GiuseppeLeotta/SkyClock32/tools/IMG_P1.jpg

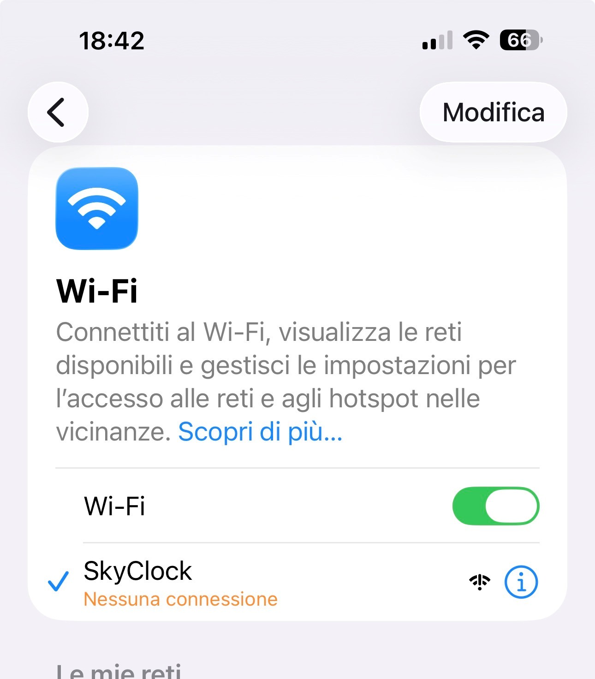
tools/IMG_P1.jpg
