GiuseppeLeotta/SkyClock32/SkyClock32/dataJupiterImg.h

#ifndef _DATA_JUPITER_IMG_H_
#define _DATA_JUPITER_IMG_H_

#include "gImage.h"

// Immagine convertita in RGB565 (148x148)
const uint16_t jupiterImg[21904] PROGMEM = {
0x0BB4, 0x0BB4, 0x0BB4, 0x0BB4, 0x0BB4, 0x0BB4, 0x0BB4, 0x0BB4, 0x0BB4, 0x0BB4, 0x0BB4, 0x0BB4, 0x0BB4, 0x0BB4, 0x0BB4, 0x0BB4, 
0x0BB4, 0x0BB4, 0x0BB4, 0x0BB4, 0x0BB4, 0x0BB4, 0x0BB4, 0x0BB4, 0x0BB4, 0x0BB4, 0x0BB4, 0x0BB4, 0x0BB4, 0x0BB4, 0x0BB4, 0x0BB4, 
0x0BB4, 0x0BB4, 0x0BB4, 0x0BB4, 0x0BB4, 0x0BB4, 0x0BB4, 0x0BB4, 0x0BB4, 0x0BB4, 0x0BB4, 0x0BB4, 0x0BB4, 0x0BB4, 0x0BB4, 0x0BB4, 
0x0BB4, 0x0BB4, 0x0BB4, 0x0BB4, 0x0BB4, 0x0BB4, 0x0BB4, 0x0BB4, 0x0BB4, 0x0BB4, 0x0BB4, 0x0BB4, 0x0BB4, 0x0BB4, 0x0BB4, 0x0BB4, 
0x0BB4, 0x0BB4, 0x0BB4, 0x0BB4, 0x0BB4, 0x0BB4, 0x0BB4, 0x0BB4, 0x0BB4, 0x0BB4, 0x0BB4, 0x0BB4, 0x0BB4, 0x0BB4, 0x0BB4, 0x0BB4, 
0x0BB4, 0x0BB4, 0x0BB4, 0x0BB4, 0x0BB4, 0x0BB4, 0x0BB4, 0x0BB4, 0x0BB4, 0x0BB4, 0x0BB4, 0x0BB4, 0x0BB4, 0x0BB4, 0x0BB4, 0x0BB4, 
0x0BB4, 0x0BB4, 0x0BB4, 0x0BB4, 0x0BB4, 0x0BB4, 0x0BB4, 0x0BB4, 0x0BB4, 0x0BB4, 0x0BB4, 0x0BB4, 0x0BB4, 0x0BB4, 0x0BB4, 0x0BB4, 
0x0BB4, 0x0BB4, 0x0BB4, 0x0BB4, 0x0BB4, 0x0BB4, 0x0BB4, 0x0BB4, 0x0BB4, 0x0BB4, 0x0BB4, 0x0BB4, 0x0BB4, 0x0BB4, 0x0BB4, 0x0BB4, 
0x0BB4, 0x0BB4, 0x0BB4, 0x0BB4, 0x0BB4, 0x0BB4, 0x0BB4, 0x0BB4, 0x0BB4, 0x0BB4, 0x0BB4, 0x0BB4, 0x0BB4, 0x0BB4, 0x0BB4, 0x0BB4, 
0x0BB4, 0x0BB4, 0x0BB4, 0x0BB4, 0x0BB4, 0x0BB4, 0x0BB4, 0x0BB4, 0x0BB4, 0x0BB4, 0x0BB4, 0x0BB4, 0x0BB4, 0x0BB4, 0x0BB4, 0x0BB4, 
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
0x0BB4, 0x0BB4, 0x0BB4, 0x0BB4, 0x0BB4, 0x0BB4, 0x0BB4, 0x0BB4, 0x0BB4, 0x0BB4, 0x0BB4, 0x0BB4, 0x0BB4, 0x0BB4, 0x0BB4, 0x0BB4, 
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

};


gImage jupiterImage {
   148,148, (uint16_t *) jupiterImg
};

#endif
