GiuseppeLeotta/SkyClock32/SkyClock32/dataMercuryImg.h

#ifndef _DATA_MERCURY_IMG_H_
#define _DATA_MERCURY_IMG_H_

#include "gImage.h"

// Immagine convertita in RGB565 (148x148)
const uint16_t mercuryImg[21904] PROGMEM = {
0x0BB4, 0x0BB4, 0x0BB4, 0x0BB4, 0x0BB4, 0x0BB4, 0x0BB4, 0x0BB4, 0x0BB4, 0x0BB4, 0x0BB4, 0x0BB4, 0x0BB4, 0x0BB4, 0x0BB4, 0x0BB4, 
0x0BB4, 0x0BB4, 0x0BB4, 0x0BB4, 0x0BB4, 0x0BB4, 0x0BB4, 0x0BB4, 0x0BB4, 0x0BB4, 0x0BB4, 0x0BB4, 0x0BB4, 0x0BB4, 0x0BB4, 0x0BB4, 
0x0BB4, 0x0BB4, 0x0BB4, 0x0BB4, 0x0BB4, 0x0BB4, 0x0BB4, 0x0BB4, 0x0BB4, 0x0BB4, 0x0BB4, 0x0BB4, 0x0BB4, 0x0BB4, 0x0BB4, 0x0BB4, 
0x0BB4, 0x0BB4, 0x0BB4, 0x0BB4, 0x0BB4, 0x0BB4, 0x0BB4, 0x0BB4, 0x0BB4, 0x0BB4, 0x0BB4, 0x0BB4, 0x0BB4, 0x0BB4, 0x0BB4, 0x0BB4, 
0x0BB4, 0x0BB4, 0x0BB4, 0x0BB4, 0x0BB4, 0x0BB4, 0x0BB4, 0x0BB4, 0x0BB4, 0x0BB4, 0x0BB4, 0x0BB4, 0x0B94, 0x0B52, 0x0BB4, 0x0BB4, 
0x0BB4, 0x0BB4, 0x0BB4, 0x0BB4, 0x0BB4, 0x0BB4, 0x0BB4, 0x0BB4, 0x0BB4, 0x0BB4, 0x0BB4, 0x0BB4, 0x0BB4, 0x0BB4, 0x0BB4, 0x0BB4, 
0x0BB4, 0x0BB4, 0x0BB4, 0x0BB4, 0x0BB4, 0x0BB4, 0x0BB4, 0x0BB4, 0x0BB4, 0x0BB4, 0x0BB4, 0x0BB4, 0x0BB4, 0x0BB4, 0x0BB4, 0x0BB4, 
0x0BB4, 0x0BB4, 0x0BB4, 0x0BB4, 0x0BB4, 0x0BB4, 0x0BB4, 0x0BB4, 0x0BB4, 0x0BB4, 0x0BB4, 0x0BB4, 0x0BB4, 0x0BB4, 0x0BB4, 0x0BB4, 
0x0BB4, 0x0BB4, 0x0BB4, 0x0BB4, 0x0BB4, 0x0BB4, 0x0BB4, 0x0BB4, 0x0BB4, 0x0BB4, 0x0BB4, 0x0BB4, 0x0BB4, 0x0BB4, 0x0BB4, 0x0BB4, 
0x0BB4, 0x0BB4, 0x0BB4, 0x0BB4, 0x0BB4, 0x0BB4, 0x0BB4, 0x0BB4, 0x0BB4, 0x0BB4, 0x0BB4, 0x0BB4, 0x0BB4, 0x0BB4, 0x0BB4, 0x0BB4, 
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
0x0BB4, 0x0BB4, 0x0BB4, 0x0BB4, 0x0BB4, 0x0BB4, 0x0BB4, 0x0BB4, 0x0BB4, 0x0BB4, 0x0BB4, 0x0BB4, 0x0BB4, 0x0BB4, 0x0BB4, 0x0BB4, 
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

};


gImage mercuryImage {
   148,148, (uint16_t *) mercuryImg
};

#endif
