GiuseppeLeotta/SkyClock32/SkyClock32/dataPressImg.h

#ifndef _DATA_PRESS_IMG_H_
#define _DATA_PRESS_IMG_H_

#include "gImage.h"


// Immagine convertita in RGB565 (64x64)
const uint16_t pressImg[4096] PROGMEM = {
0x0BB4, 0x0BB4, 0x0BB4, 0x0BB4, 0x0BB4, 0x0BB4, 0x0BB4, 0x0BB4, 0x0BB4, 0x0BD4, 0x3C96, 0x5CF9, 0x3C38, 0x64DA, 0x751A, 0x751A, 
0x6D1A, 0x6D1A, 0x6D1A, 0x6D1A, 0x6D1A, 0x6D1A, 0x6D1A, 0x6D1A, 0x6D1A, 0x6D1A, 0x6D1A, 0x6D1A, 0x6D1A, 0x6D1A, 0x6D1A, 0x6D1A, 
0x6CFA, 0x6CFA, 0x6CFA, 0x6CFA, 0x6CFA, 0x6CFA, 0x6CFA, 0x6CFA, 0x6CFA, 0x6CFA, 0x6CFA, 0x6CFB, 0x6CFB, 0x6CFB, 0x6CFA, 0x6CFA, 
0x6CFA, 0x6CFA, 0x6CDB, 0x4458, 0x54B8, 0x54D8, 0x1BF5, 0x0BB4, 0x0BB4, 0x0BB4, 0x0BB4, 0x0BB4, 0x0BB4, 0x0BB4, 0x0BB4, 0x0BB4, 
0x0BB4, 0x0BB4, 0x0BB4, 0x0BB4, 0x0BB4, 0x0BB4, 0x0BB4, 0x2C35, 0x54B9, 0x8D7C, 0x7D3D, 0x751E, 0x6CFD, 0x74FE, 0x6CFD, 0x6CFD, 
0x6CFD, 0x6CFE, 0x6CFE, 0x6CFE, 0x6CFE, 0x6CDE, 0x6CDE, 0x6CDE, 0x6CDE, 0x6CDE, 0x6CDE, 0x6CDE, 0x6CDE, 0x6CDE, 0x6CDE, 0x6CDE, 
0x64DD, 0x64DE, 0x64DE, 0x64DE, 0x64BE, 0x64DD, 0x64DD, 0x64DD, 0x64BD, 0x64BD, 0x64BD, 0x64BD, 0x64BD, 0x64BD, 0x64BD, 0x64BD, 
0x64BD, 0x5C9D, 0x649D, 0x5C9D, 0x64BD, 0x6CBD, 0x74FD, 0x7D5B, 0x3C76, 0x0BB4, 0x0BB4, 0x0BB4, 0x0BB4, 0x0BB4, 0x0BB4, 0x0BB4, 
0x0BB4, 0x0BB4, 0x0BB4, 0x0BB4, 0x0BB4, 0x13D4, 0x6D19, 0x855D, 0x6CFD, 0x5C9D, 0x5C9E, 0x5C9D, 0x5C9D, 0x5C9E, 0x5C9D, 0x5C9D, 
0x5C7D, 0x5C7E, 0x5C7E, 0x5C7E, 0x5C7D, 0x5C7D, 0x5C7D, 0x5C7D, 0x5C7D, 0x547D, 0x547D, 0x547D, 0x547D, 0x545D, 0x545D, 0x545D, 
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
0x441E, 0x441D, 0x441D, 0x441D, 0x441D, 0x441D, 0x441D, 0x43FD, 0x43FD, 0x43FD, 0x43FD, 0x43FD, 0x43FD, 0x43FC, 0x857C, 0x0BB4, 
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

};


gImage pressImage {
   64,64, (uint16_t *) pressImg
};
#endif  
